wszeto9/DGFF-GPU-Adapter/PCB Rev A/DGFF.kicad_sch

## KiCad design PCB Rev A/DGFF.kicad_sch (2024-08-07)

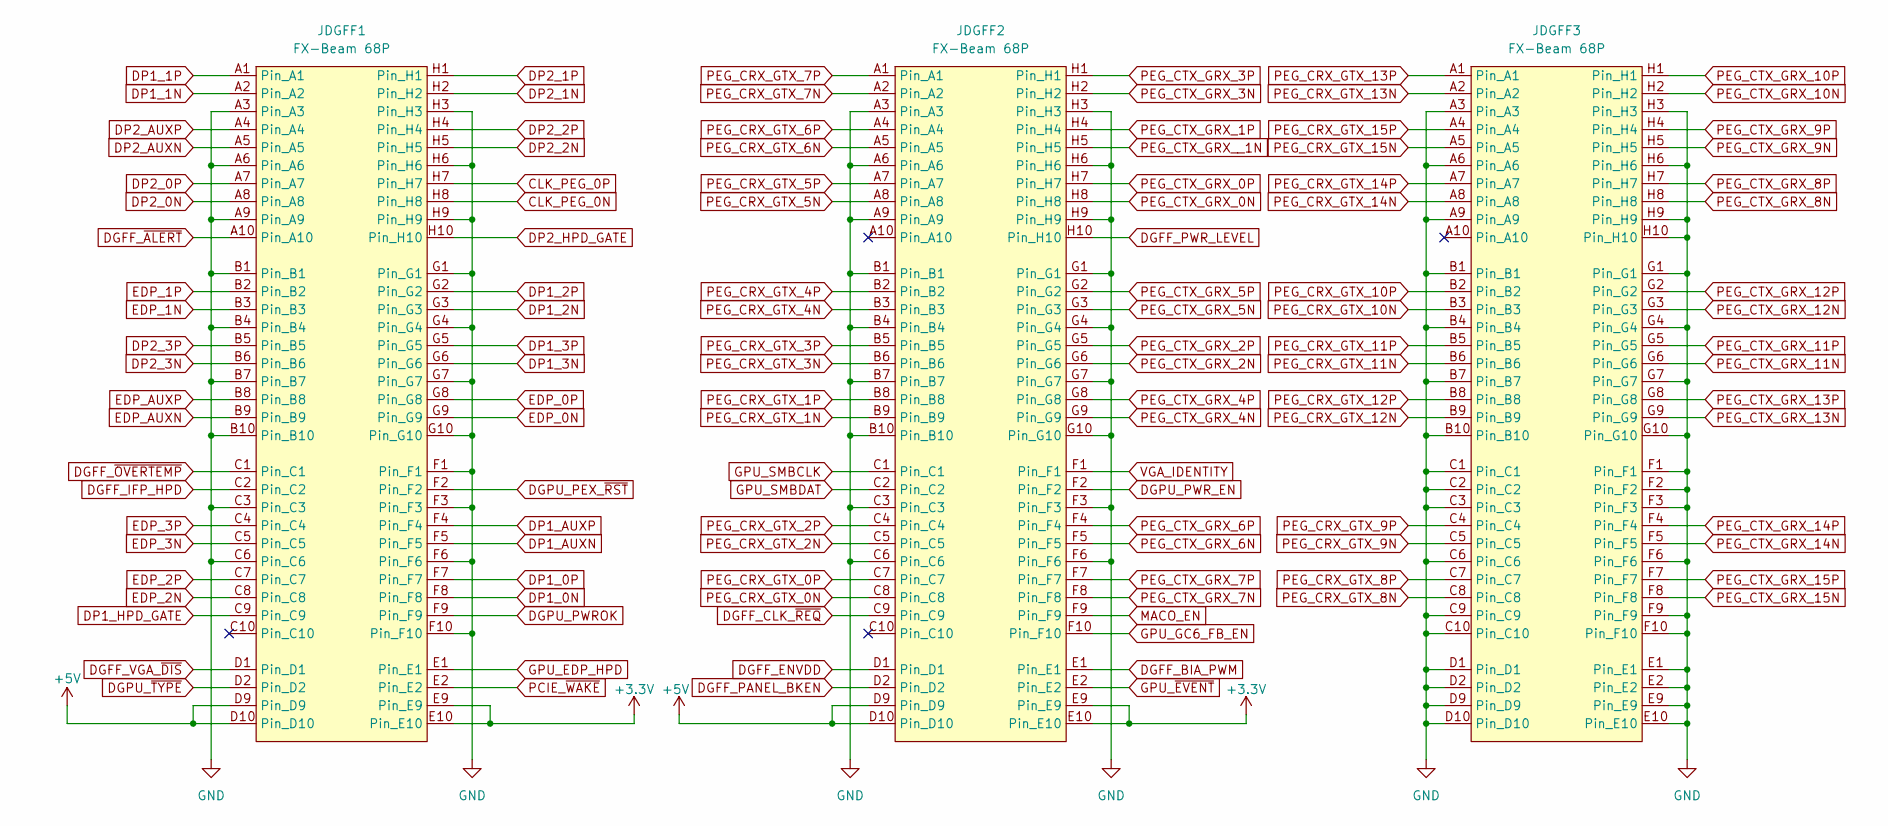
[picture p6: schematic DGFF.kicad_sch]

Parts:
JDGFF1, JDGFF2, JDGFF3: FX-Beam 68P; FXBeam_68P

Connections:
+3.3V: JDGFF1.E9, JDGFF1.E10, JDGFF2.E9, JDGFF2.E10
+5V: JDGFF1.D9, JDGFF1.D10, JDGFF2.D9, JDGFF2.D10
CLK_PEG_0N: JDGFF1.H8
CLK_PEG_0P: JDGFF1.H7
DGFF_BIA_PWM: JDGFF2.E1
DGFF_CLK_~REQ: JDGFF2.C9
DGFF_ENVDD: JDGFF2.D1
DGFF_IFP_HPD: JDGFF1.C2
DGFF_PANEL_BKEN: JDGFF2.D2
DGFF_PWR_LEVEL: JDGFF2.H10
DGFF_VGA_~DIS: JDGFF1.D1
DGFF_~ALERT: JDGFF1.A10
DGFF_~OVERTEMP: JDGFF1.C1
DGPU_PEX_~RST: JDGFF1.F2
DGPU_PWROK: JDGFF1.F9
DGPU_PWR_EN: JDGFF2.F2
DGPU_~TYPE: JDGFF1.D2
DP1_0N: JDGFF1.F8
DP1_0P: JDGFF1.F7
DP1_1N: JDGFF1.A2
DP1_1P: JDGFF1.A1
DP1_2N: JDGFF1.G3
DP1_2P: JDGFF1.G2
DP1_3N: JDGFF1.G6
DP1_3P: JDGFF1.G5
DP1_AUXN: JDGFF1.F5
DP1_AUXP: JDGFF1.F4
DP1_HPD_GATE: JDGFF1.C9
DP2_0N: JDGFF1.A8
DP2_0P: JDGFF1.A7
DP2_1N: JDGFF1.H2
DP2_1P: JDGFF1.H1
DP2_2N: JDGFF1.H5
DP2_2P: JDGFF1.H4
DP2_3N: JDGFF1.B6
DP2_3P: JDGFF1.B5
DP2_AUXN: JDGFF1.A5
DP2_AUXP: JDGFF1.A4
DP2_HPD_GATE: JDGFF1.H10
EDP_0N: JDGFF1.G9
EDP_0P: JDGFF1.G8
EDP_1N: JDGFF1.B3
EDP_1P: JDGFF1.B2
EDP_2N: JDGFF1.C8
EDP_2P: JDGFF1.C7
EDP_3N: JDGFF1.C5
EDP_3P: JDGFF1.C4
EDP_AUXN: JDGFF1.B9
EDP_AUXP: JDGFF1.B8
GND: JDGFF1.A3, JDGFF1.A6, JDGFF1.A9, JDGFF1.B1, JDGFF1.B4, JDGFF1.B7, JDGFF1.B10, JDGFF1.C3, JDGFF1.C6, JDGFF1.F1, JDGFF1.F3, JDGFF1.F6, JDGFF1.F10, JDGFF1.G1, JDGFF1.G4, JDGFF1.G7, JDGFF1.G10, JDGFF1.H3, JDGFF1.H6, JDGFF1.H9, JDGFF2.A3, JDGFF2.A6, JDGFF2.A9, JDGFF2.B1, JDGFF2.B4, JDGFF2.B7, JDGFF2.B10, JDGFF2.C3, JDGFF2.C6, JDGFF2.F3, JDGFF2.F6, JDGFF2.G1, JDGFF2.G4, JDGFF2.G7, JDGFF2.G10, JDGFF2.H3, JDGFF2.H6, JDGFF2.H9, JDGFF3.A3, JDGFF3.A6, JDGFF3.A9, JDGFF3.B1, JDGFF3.B4, JDGFF3.B7, JDGFF3.B10, JDGFF3.C1, JDGFF3.C2, JDGFF3.C3, JDGFF3.C6, JDGFF3.C9, JDGFF3.C10, JDGFF3.D1, JDGFF3.D2, JDGFF3.D9, JDGFF3.D10, JDGFF3.E1, JDGFF3.E2, JDGFF3.E9, JDGFF3.E10, JDGFF3.F1, JDGFF3.F2, JDGFF3.F3, JDGFF3.F6, JDGFF3.F9, JDGFF3.F10, JDGFF3.G1, JDGFF3.G4, JDGFF3.G7, JDGFF3.G10, JDGFF3.H3, JDGFF3.H6, JDGFF3.H9, JDGFF3.H10
GPU_EDP_HPD: JDGFF1.E1
GPU_GC6_FB_EN: JDGFF2.F10
GPU_SMBCLK: JDGFF2.C1
GPU_SMBDAT: JDGFF2.C2
GPU_~EVENT: JDGFF2.E2
MACO_EN: JDGFF2.F9
PCIE_~WAKE: JDGFF1.E2
PEG_CRX_GTX_0N: JDGFF2.C8
PEG_CRX_GTX_0P: JDGFF2.C7
PEG_CRX_GTX_1N: JDGFF2.B9
PEG_CRX_GTX_1P: JDGFF2.B8
PEG_CRX_GTX_2N: JDGFF2.C5
PEG_CRX_GTX_2P: JDGFF2.C4
PEG_CRX_GTX_3N: JDGFF2.B6
PEG_CRX_GTX_3P: JDGFF2.B5
PEG_CRX_GTX_4N: JDGFF2.B3
PEG_CRX_GTX_4P: JDGFF2.B2
PEG_CRX_GTX_5N: JDGFF2.A8
PEG_CRX_GTX_5P: JDGFF2.A7
PEG_CRX_GTX_6N: JDGFF2.A5
PEG_CRX_GTX_6P: JDGFF2.A4
PEG_CRX_GTX_7N: JDGFF2.A2
PEG_CRX_GTX_7P: JDGFF2.A1
PEG_CRX_GTX_8N: JDGFF3.C8
PEG_CRX_GTX_8P: JDGFF3.C7
PEG_CRX_GTX_9N: JDGFF3.C5
PEG_CRX_GTX_9P: JDGFF3.C4
PEG_CRX_GTX_10N: JDGFF3.B3
PEG_CRX_GTX_10P: JDGFF3.B2
PEG_CRX_GTX_11N: JDGFF3.B6
PEG_CRX_GTX_11P: JDGFF3.B5
PEG_CRX_GTX_12N: JDGFF3.B9
PEG_CRX_GTX_12P: JDGFF3.B8
PEG_CRX_GTX_13N: JDGFF3.A2
PEG_CRX_GTX_13P: JDGFF3.A1
PEG_CRX_GTX_14N: JDGFF3.A8
PEG_CRX_GTX_14P: JDGFF3.A7
PEG_CRX_GTX_15N: JDGFF3.A5
PEG_CRX_GTX_15P: JDGFF3.A4
PEG_CTX_GRX_0N: JDGFF2.H8
PEG_CTX_GRX_0P: JDGFF2.H7
PEG_CTX_GRX_1P: JDGFF2.H4
PEG_CTX_GRX_2N: JDGFF2.G6
PEG_CTX_GRX_2P: JDGFF2.G5
PEG_CTX_GRX_3N: JDGFF2.H2
PEG_CTX_GRX_3P: JDGFF2.H1
PEG_CTX_GRX_4N: JDGFF2.G9
PEG_CTX_GRX_4P: JDGFF2.G8
PEG_CTX_GRX_5N: JDGFF2.G3
PEG_CTX_GRX_5P: JDGFF2.G2
PEG_CTX_GRX_6N: JDGFF2.F5
PEG_CTX_GRX_6P: JDGFF2.F4
PEG_CTX_GRX_7N: JDGFF2.F8
PEG_CTX_GRX_7P: JDGFF2.F7
PEG_CTX_GRX_8N: JDGFF3.H8
PEG_CTX_GRX_8P: JDGFF3.H7
PEG_CTX_GRX_9N: JDGFF3.H5
PEG_CTX_GRX_9P: JDGFF3.H4
PEG_CTX_GRX_10N: JDGFF3.H2
PEG_CTX_GRX_10P: JDGFF3.H1
PEG_CTX_GRX_11N: JDGFF3.G6
PEG_CTX_GRX_11P: JDGFF3.G5
PEG_CTX_GRX_12N: JDGFF3.G3
PEG_CTX_GRX_12P: JDGFF3.G2
PEG_CTX_GRX_13N: JDGFF3.G9
PEG_CTX_GRX_13P: JDGFF3.G8
PEG_CTX_GRX_14N: JDGFF3.F5
PEG_CTX_GRX_14P: JDGFF3.F4
PEG_CTX_GRX_15N: JDGFF3.F8
PEG_CTX_GRX_15P: JDGFF3.F7
PEG_CTX_GRX__1N: JDGFF2.H5
VGA_IDENTITY: JDGFF2.F1
