wszeto9/DGFF-GPU-Adapter/PCB Rev A/DGFFAdapter.kicad_sch

## KiCad design PCB Rev A/DGFFAdapter.kicad_sch (2024-08-07)

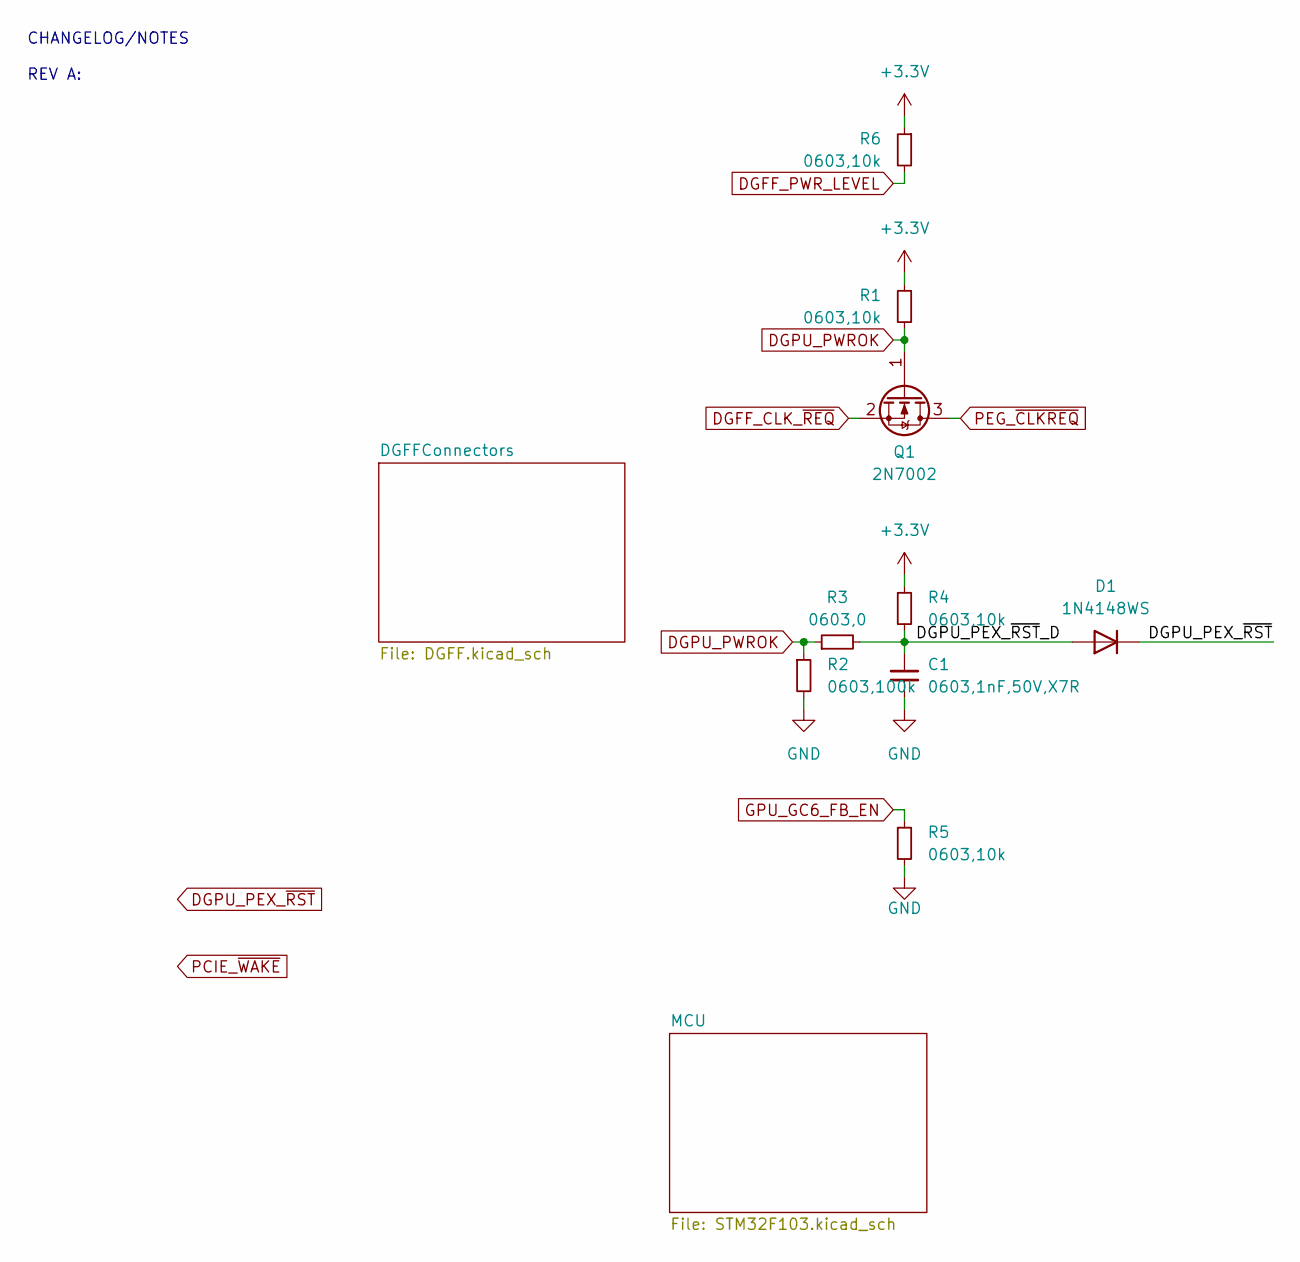
[picture p7: schematic DGFFAdapter.kicad_sch]

Parts:
C1: 0603,1nF,50V,X7R; C_0603_1608Metric; MFGPN CL10B102KB8NNNC; LCSC C1588
D1: 1N4148WS; D_SOD-323
Q1: 2N7002; SOT-23
R1, R4, R5, R6: 0603,10k; R_0603_1608Metric; MFGPN 0603WAF1002T5E; LCSC C25804
R2: 0603,100k; R_0603_1608Metric; MFGPN 0603WAF1003T5E; LCSC C25803
R3: 0603,0; R_0603_1608Metric; MFGPN 0603WAF0000T5E; LCSC C21189

Connections:
+3.3V: R1.1, R4.1, R6.1
DGFF_CLK_~REQ: Q1.2 (S)
DGFF_PWR_LEVEL: R6.2
DGPU_PEX_~RST: D1.1 (K)
DGPU_PEX_~RST_D: C1.1, D1.2 (A), R3.2, R4.2
DGPU_PWROK: Q1.1 (G), R1.2, R2.1, R3.1
GND: C1.2, R2.2, R5.2
GPU_GC6_FB_EN: R5.1
PEG_~CLKREQ: Q1.3 (D)

Notes on the sheet:
CHANGELOG/NOTES REV A:
